zarif98/ECE4180RCProject/schematics/mbed sonar.sch

## EAGLE design schematics/mbed sonar.sch (2021-05-03)

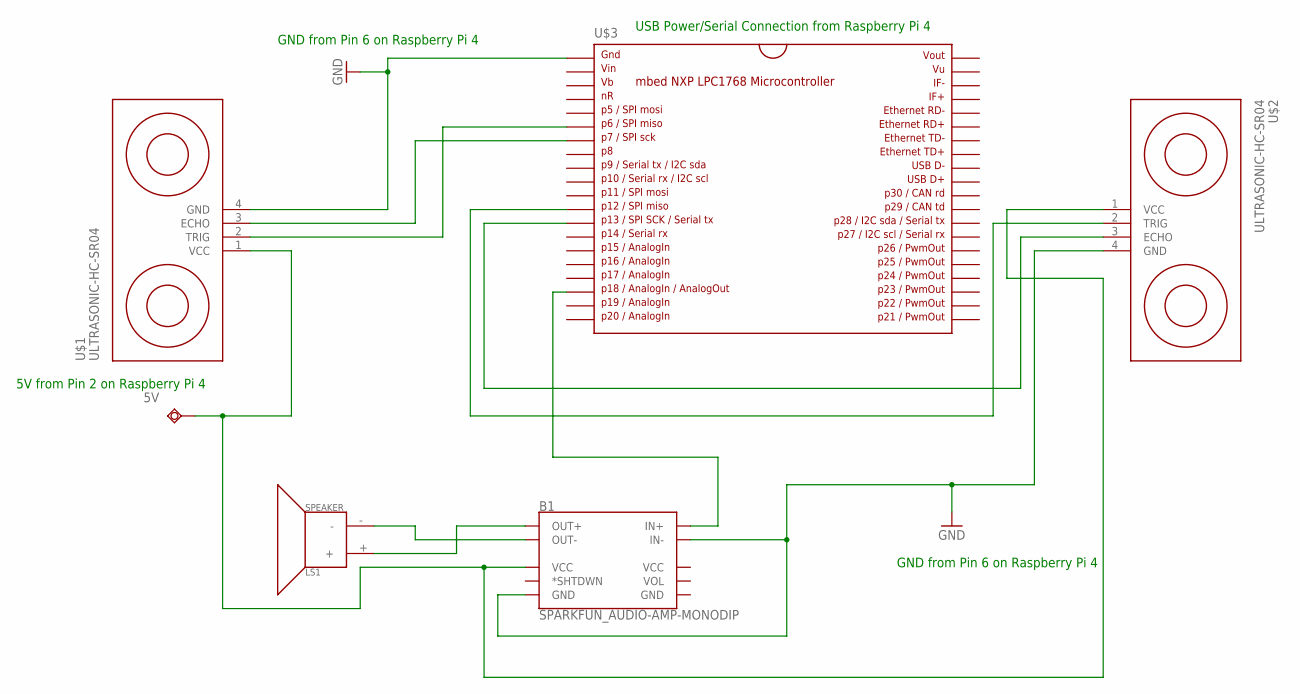
[picture p8: schematic mbed sonar.sch]

Parts:
5V: TPSQPAD1-20; P1-20
B1: SPARKFUN_AUDIO-AMP-MONODIP; AUDIO-AMP-MONO
LS1: SPEAKER; PCB_MOUNT_SPEAKER
U$1, U$2: ULTRASONIC-HC-SR04
U$3: MBED1768; DIL40_0.9

Connections:
GND: B1.IN-, B1.PWR- (GND), U$1.4 (GND), U$2.4 (GND), U$3.1
unnamed: B1.IN+, U$3.18
unnamed: B1.OUT+, LS1.+
unnamed: B1.OUT-, LS1.-
unnamed: 5V.TP, B1.PWR+ (VCC), U$1.1 (VCC), U$2.1 (VCC)
unnamed: U$1.2 (TRIG), U$3.6
unnamed: U$1.3 (ECHO), U$3.7
unnamed: U$2.2 (TRIG), U$3.12
unnamed: U$2.3 (ECHO), U$3.13

Notes on the sheet:
GND from Pin 6 on Raspberry Pi 4
5V from Pin 2 on Raspberry Pi 4
USB Power/Serial Connection from Raspberry Pi 4
