zarif98/ECE4180RCProject/schematics/motor mbed.sch

## EAGLE design schematics/motor mbed.sch (2021-05-03)

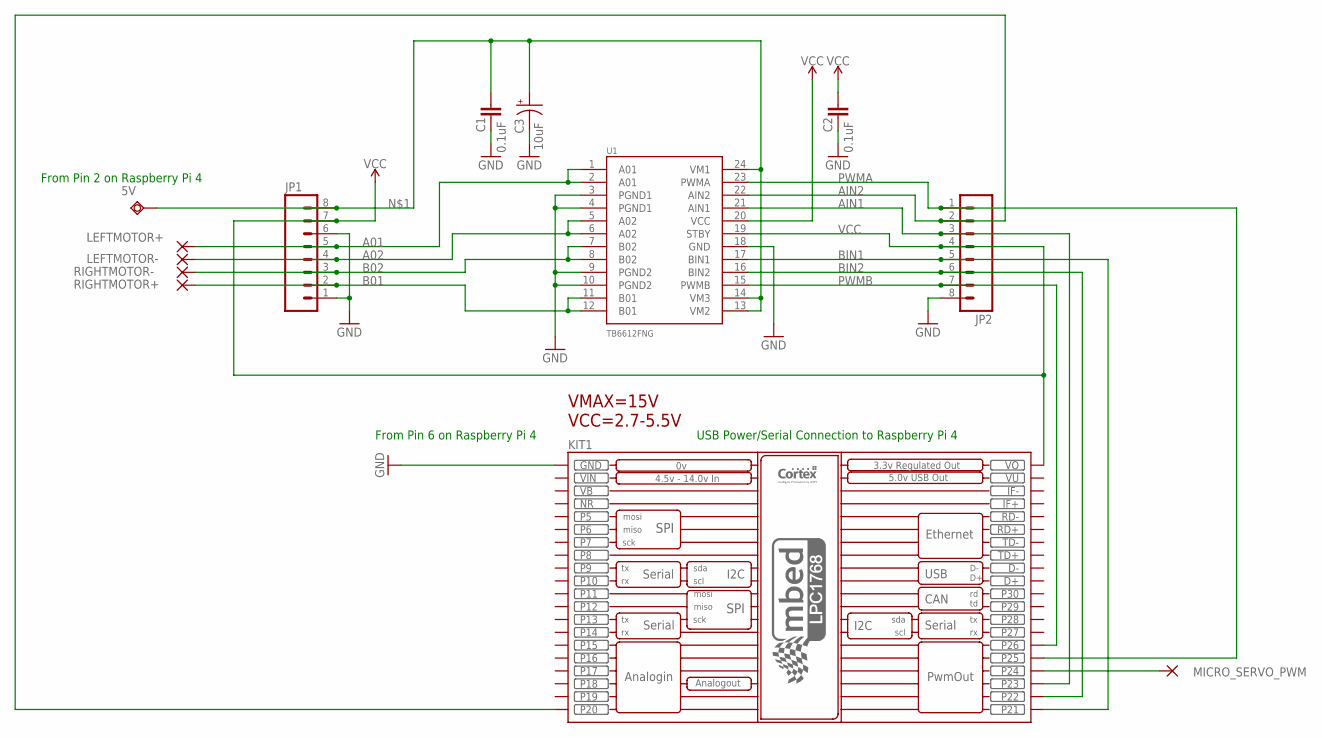
[picture p9: schematic motor mbed.sch]

Parts:
5V: TPSQPAD1-20; P1-20
C1, C2: 0.1uF; 0402
C3: 10uF; EIA3528
JP1, JP2: M0875_PERCENT_REDUCED; 1X08_OFFSET_REDUCED
KIT1: MBED_NXP_LPC1768; MBED-KIT
LEFTMOTOR+: WIREPAD2,54/1,1; 2,54/1,1
LEFTMOTOR-: WIREPAD2,54/1,1; 2,54/1,1
MICRO_SERVO_PWM: WIREPAD2,54/1,1; 2,54/1,1
RIGHTMOTOR+: WIREPAD2,54/1,1; 2,54/1,1
RIGHTMOTOR-: WIREPAD2,54/1,1; 2,54/1,1
U1: TB6612FNG; SSOP24

Connections:
A01: JP1.5, LEFTMOTOR+.1, U1.1 (A01), U1.2 (A01)
A02: JP1.4, LEFTMOTOR-.1, U1.5 (A02), U1.6 (A02)
AIN1: JP2.3, KIT1.P$23 (P23), U1.21 (AIN1)
AIN2: JP2.2, KIT1.P$20 (P20), U1.22 (AIN2)
B01: JP1.2, RIGHTMOTOR+.1, U1.11 (B01), U1.12 (B01)
B02: JP1.3, RIGHTMOTOR-.1, U1.7 (B02), U1.8 (B02)
BIN1: JP2.5, KIT1.P$21 (P21), U1.17 (BIN1)
BIN2: JP2.6, KIT1.P$22 (P22), U1.16 (BIN2)
GND: C1.2, C2.2, C3.C (-), JP1.1, JP1.6, JP2.8, KIT1.GND, U1.3 (PGND1), U1.4 (PGND1), U1.9 (PGND2), U1.10 (PGND2), U1.18 (GND)
unnamed: 5V.TP, C1.1, C3.A (+), JP1.8, U1.13 (VM2), U1.14 (VM3), U1.24 (VM1)
unnamed: KIT1.P$24 (P24), MICRO_SERVO_PWM.1
PWMA: JP2.1, KIT1.P$25 (P25), U1.23 (PWMA)
PWMB: JP2.7, KIT1.P$26 (P26), U1.15 (PWMB)
VCC: C2.1, JP1.7, JP2.4, KIT1.VOUT (VO), U1.19 (STBY), U1.20 (VCC)

Notes on the sheet:
VMAX=15V VCC=2.7-5.5V
From Pin 2 on Raspberry Pi 4
From Pin 6 on Raspberry Pi 4
USB Power/Serial Connection to Raspberry Pi 4
